josero360/mt2_devboard_und_fachartikel/Simulation/TEst.asc

C1: cap; 1µ
M1: nmos; IRFP240
R1: res; 0.1
R2: res; 5000; tol=0
R3: res; 5000; tol=1
R4: res; 5000; tol=1
R5: res; 20000; tol=1
R6: res; 15000
R7: res; 0
R8: res; 5000
R10: res; 0
U1: AD820
U2: AD820
U4: LTC2057
U5: LTC2057
V1: voltage; PWL(0 20 0.1 20 0.12 10 0.14 14 0.19 0); Rser=0
V2: voltage; 12
V3: voltage; PWL(0 0 0.05 0.5 0.07 0.4 0.09 0.7 0.2 0.7)
V4: voltage; 15
V5: voltage; 15
V6: voltage; 5
Named nets: 0, Last, Q1_Gate, R1.inv, R1.ninv, U1+, R1
.tran 200ms startup
